c0de111/inki/images/4_2_white_pages/esign_4_2_page_3.JPG

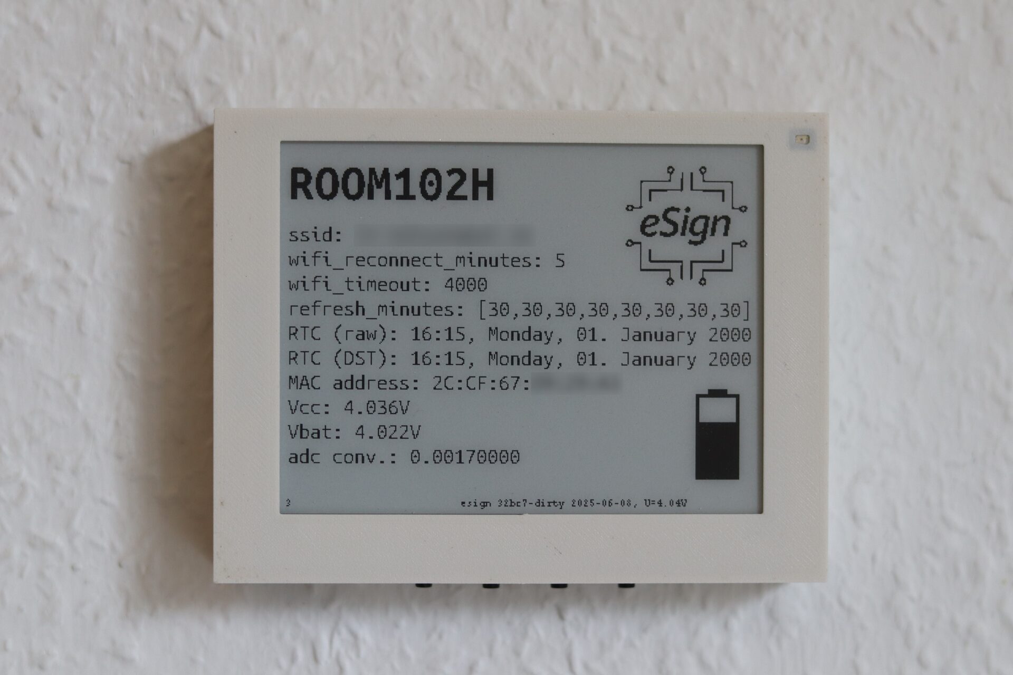
images/4_2_white_pages/esign_4_2_page_3.JPG
