c0de111/inki/images/7_5_ccu-historian.JPG

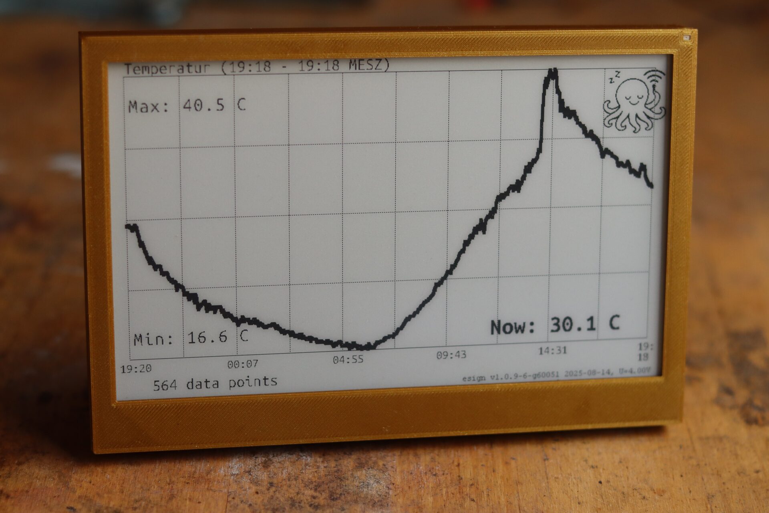
images/7_5_ccu-historian.JPG
