c0de111/inki/images/esign_4_2_backside.JPG

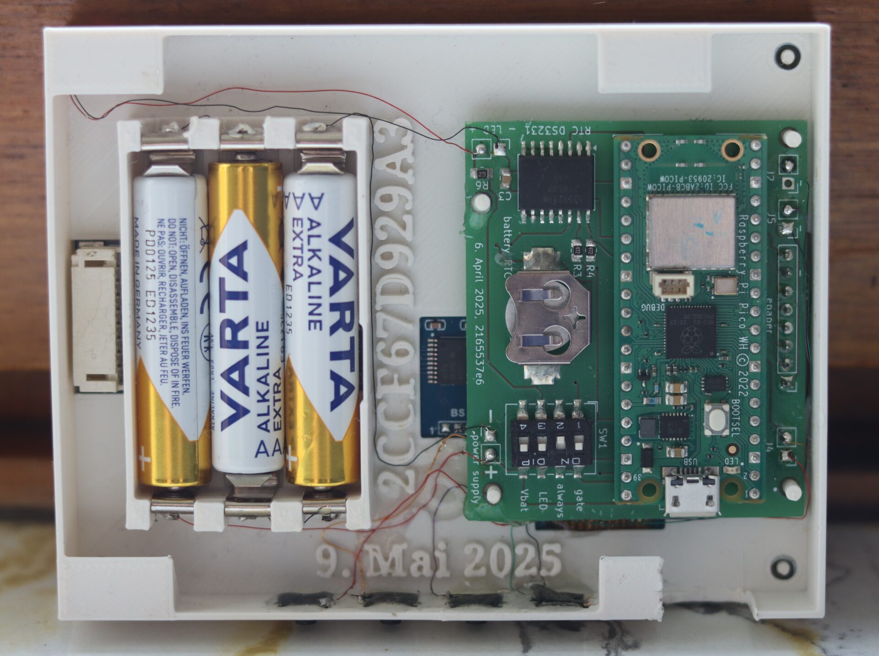
images/esign_4_2_backside.JPG
