c0de111/inki/images/esign_4_2_video_refresh_screenshot.png

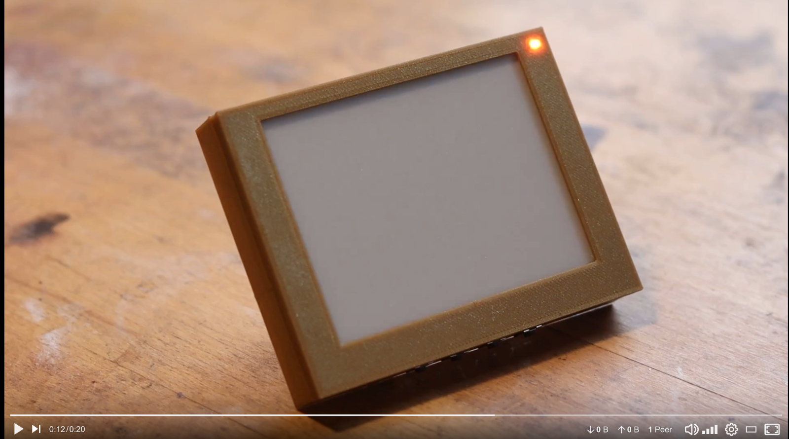
images/esign_4_2_video_refresh_screenshot.png
