c0de111/inki/images/esign_4_2_video_screenshot.jpg

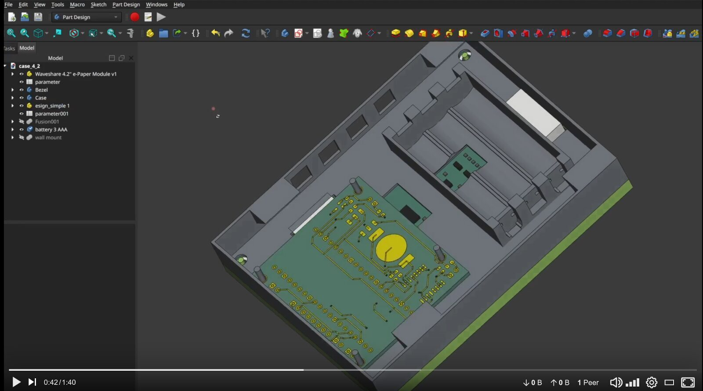
images/esign_4_2_video_screenshot.jpg
