c0de111/inki/images/inki_octopus.png

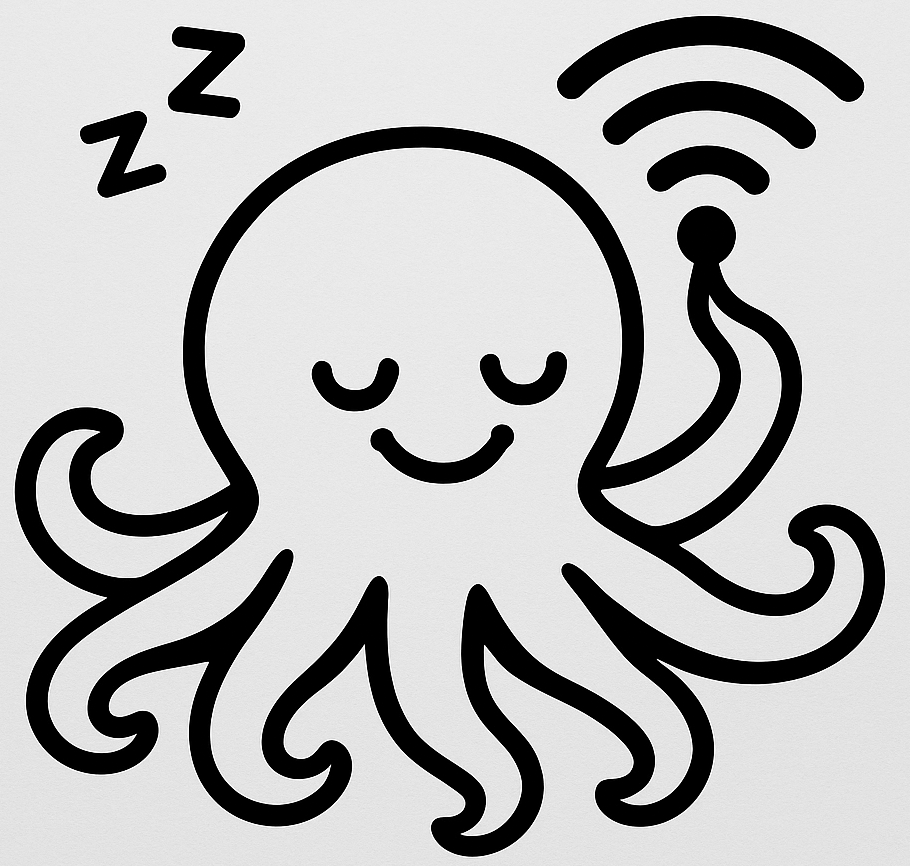
images/inki_octopus.png
