c0de111/inki/images/inki_webinterface_landingpage_combined.png

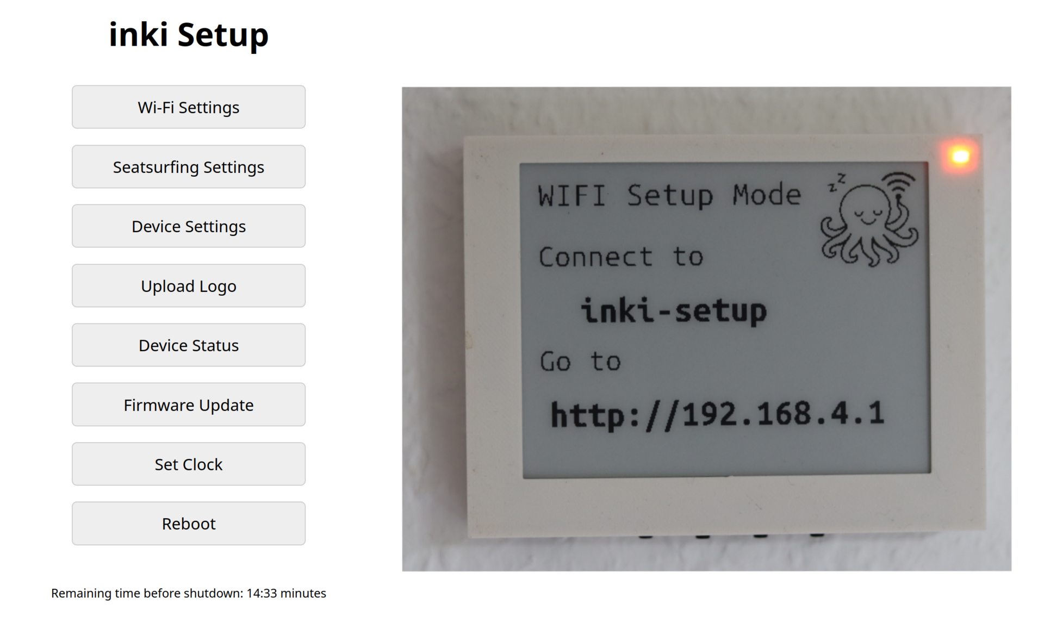
images/inki_webinterface_landingpage_combined.png
