c0de111/inki/images/log_prototype_esign_7_5.png

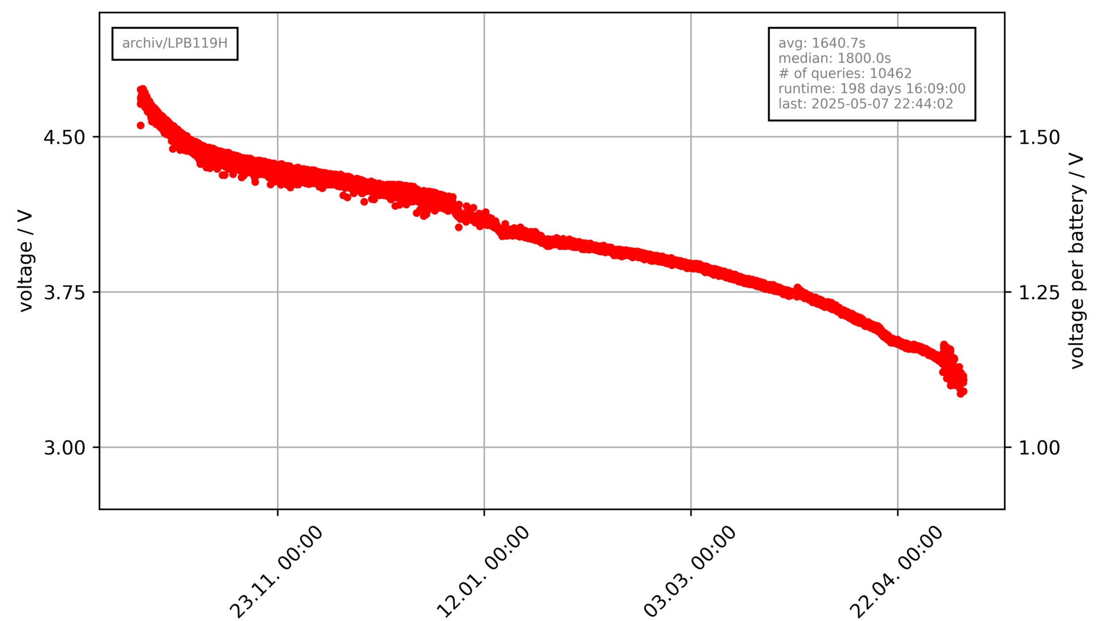
images/log_prototype_esign_7_5.png
