c0de111/inki/firmware/c/ImageResources.c

#include "ImageResources.h"

// Image arrays and constants
const SubImage battery_levels_64x97[] = {
    { .data = gImage_battery_level_1, .width = 64, .height = 97 },
    { .data = gImage_battery_level_2, .width = 64, .height = 97 },
    { .data = gImage_battery_level_3, .width = 64, .height = 97 },
    { .data = gImage_battery_level_4, .width = 64, .height = 97 },
    { .data = gImage_battery_level_5, .width = 64, .height = 97 },
    { .data = gImage_battery_level_6, .width = 64, .height = 97 },
    { .data = gImage_battery_level_7, .width = 64, .height = 97 },
    { .data = gImage_battery_level_8, .width = 64, .height = 97 },
    { .data = gImage_battery_level_9, .width = 64, .height = 97 },
    { .data = gImage_battery_level_10, .width = 64, .height = 97 },
};

const SubImage inki_octopus_100_95 = {
    .data = gImage_inki_octopus_100_95,
    .width = 104,
    .height = 95
};

const SubImage qr_github_link = {
    .data = gImage_github_link,
    .width = 56,
    .height = 50
};

const unsigned char gImage_battery_level_1[776] = {
    0x00, 0x00, 0x00, 0x00, 0x00, 0x00, 0x00, 0x00, 0x00, 0x00, 0x00, 0x00, 0x00, 0x00, 0x00, 0x00,
    0x00, 0x00, 0x00, 0x00, 0x00, 0x00, 0x00, 0x00, 0x00, 0x00, 0x00, 0x00, 0x00, 0x00, 0x00, 0x00,
    0x00, 0x00, 0x00, 0x00, 0x00, 0x00, 0x00, 0x00, 0x00, 0x00, 0x00, 0x00, 0x00, 0x00, 0x00, 0x00,
    0x00, 0x00, 0x00, 0x00, 0x00, 0x00, 0x00, 0x00, 0x00, 0x00, 0x00, 0x00, 0x00, 0x00, 0x00, 0x00,
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
    0x00, 0x00, 0x00, 0x00, 0x06, 0x00, 0x18, 0x60, 0x03, 0xF8, 0x0C, 0x01, 0x83, 0x00, 0x00, 0x00,
    0x00, 0x06, 0x00, 0x0F, 0xC0, 0x01, 0xF0, 0x0C, 0x01, 0x83, 0x00, 0x00, 0x00, 0x00, 0x06, 0x00,
    0x07, 0x80, 0x00, 0x00, 0x18, 0x03, 0x03, 0x00, 0x00, 0x01, 0xF0, 0x03, 0x00, 0x00, 0x00, 0x00,
    0x00, 0x18, 0x07, 0x02, 0x00, 0x00, 0x07, 0xF8, 0x03, 0x00, 0x00, 0x00, 0x00, 0x00, 0x18, 0x06,
    0x06, 0x00, 0x00, 0x0E, 0x18, 0x03, 0x80, 0x00, 0x60, 0x03, 0x00, 0x30, 0x1C, 0x06, 0x00, 0x00,
    0x1C, 0x38, 0x01, 0x80, 0x00, 0x60, 0x03, 0x00, 0x30, 0x38, 0x0C, 0x00, 0x00, 0x18, 0x70, 0x01,
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
};
