c0de111/inki/firmware/c/rv3028.c

#include "rv3028.h"

#include <stddef.h>
#include <string.h>

#define RV3028_REG_SECONDS 0x00u
#define RV3028_REG_MINUTES 0x01u
#define RV3028_REG_HOURS 0x02u
#define RV3028_REG_WEEKDAY 0x03u
#define RV3028_REG_DATE 0x04u
#define RV3028_REG_MONTH 0x05u
#define RV3028_REG_YEAR 0x06u

#define RV3028_REG_MINUTES_ALARM 0x07u
#define RV3028_REG_HOURS_ALARM 0x08u
#define RV3028_REG_WEEKDAY_DATE_ALARM 0x09u

#define RV3028_REG_STATUS 0x0Eu
#define RV3028_REG_CONTROL1 0x0Fu
#define RV3028_REG_CONTROL2 0x10u
#define RV3028_REG_EEPROM_BACKUP 0x37u
#define RV3028_REG_ID 0x28u

#define RV3028_STATUS_AF_BIT (1u << 2)

#define RV3028_CONTROL1_WADA_BIT (1u << 5)
#define RV3028_CONTROL2_AIE_BIT (1u << 3)
#define RV3028_CONTROL2_12_24_BIT (1u << 1)

#define RV3028_BACKUP_FEDE_BIT (1u << 4)
#define RV3028_BACKUP_BSM_MASK (3u << 2)
#define RV3028_BACKUP_BSM_LSM (3u << 2)

static uint8_t bcd_to_bin(uint8_t value) {
    return (uint8_t)(((value >> 4u) * 10u) + (value & 0x0Fu));
}

static uint8_t bin_to_bcd(uint8_t value) {
    return (uint8_t)(((value / 10u) << 4u) | (value % 10u));
}

static bool bcd_value_in_range(uint8_t bcd, uint8_t min_value, uint8_t max_value) {
    const uint8_t low = (uint8_t)(bcd & 0x0Fu);
    const uint8_t high = (uint8_t)((bcd >> 4u) & 0x0Fu);
    if (low > 9u || high > 9u) {
        return false;
    }

    const uint8_t value = bcd_to_bin(bcd);
    return (value >= min_value) && (value <= max_value);
}

static int rv3028_read_bytes(rv3028_t *rtc, uint8_t reg, uint8_t *data, size_t len) {
    if (!rtc || !rtc->i2c || !data || len == 0u) {
        return -1;
    }

    const int write_rc = i2c_write_blocking(rtc->i2c, rtc->addr, &reg, 1, true);
    if (write_rc != 1) {
        return -2;
    }

    const int read_rc = i2c_read_blocking(rtc->i2c, rtc->addr, data, len, false);
    if (read_rc != (int)len) {
        return -3;
    }

    return 0;
}

static int rv3028_write_bytes(rv3028_t *rtc, uint8_t reg, const uint8_t *data, size_t len) {
    if (!rtc || !rtc->i2c || !data || len == 0u || len > 15u) {
        return -1;
    }

    uint8_t buffer[16];
    buffer[0] = reg;
    memcpy(&buffer[1], data, len);

    const int write_rc = i2c_write_blocking(rtc->i2c, rtc->addr, buffer, len + 1u, false);
    if (write_rc != (int)(len + 1u)) {
        return -2;
    }

    return 0;
}

static int rv3028_read_u8(rv3028_t *rtc, uint8_t reg, uint8_t *value) {
    return rv3028_read_bytes(rtc, reg, value, 1u);
}

static int rv3028_write_u8(rv3028_t *rtc, uint8_t reg, uint8_t value) {
    return rv3028_write_bytes(rtc, reg, &value, 1u);
}

static int rv3028_configure_backup_switchover(rv3028_t *rtc) {
    uint8_t backup = 0u;
    int rc = rv3028_read_u8(rtc, RV3028_REG_EEPROM_BACKUP, &backup);
    if (rc != 0) {
        return rc;
    }

    uint8_t updated = backup;
    updated = (uint8_t)(updated | RV3028_BACKUP_FEDE_BIT);               // FEDE = 1
    updated = (uint8_t)((updated & (uint8_t)(~RV3028_BACKUP_BSM_MASK)) | // BSM = 11 (LSM)
                        RV3028_BACKUP_BSM_LSM);

    if (updated == backup) {
        return 0;
    }

    return rv3028_write_u8(rtc, RV3028_REG_EEPROM_BACKUP, updated);
}

int rv3028_init(rv3028_t *rtc, i2c_inst_t *i2c, uint8_t addr) {
    if (!rtc || !i2c) {
        return -1;
    }

    rtc->i2c = i2c;
    rtc->addr = (addr == 0u) ? RV3028_ADDR_DEFAULT : addr;
    const int rc = rv3028_configure_backup_switchover(rtc);
    if (rc != 0) {
        return rc;
    }
    return 0;
}

int rv3028_read_time(rv3028_t *rtc, rv3028_time_t *time_data) {
    if (!time_data) {
        return -1;
    }

    uint8_t raw[7] = {0};
    int rc = rv3028_read_bytes(rtc, RV3028_REG_SECONDS, raw, sizeof(raw));
    if (rc != 0) {
        return rc;
    }

    uint8_t control2 = 0u;
    rc = rv3028_read_u8(rtc, RV3028_REG_CONTROL2, &control2);
    if (rc != 0) {
        return rc;
    }
    const bool use_12h_mode = (control2 & RV3028_CONTROL2_12_24_BIT) != 0u;

    const uint8_t sec_bcd = (uint8_t)(raw[0] & 0x7Fu);
    const uint8_t min_bcd = (uint8_t)(raw[1] & 0x7Fu);
    if (!bcd_value_in_range(sec_bcd, 0u, 59u) || !bcd_value_in_range(min_bcd, 0u, 59u)) {
        return -4;
    }

    uint8_t hour = 0u;
    if (use_12h_mode) {
        const bool is_pm = (raw[2] & 0x20u) != 0u;
        const uint8_t hour12_bcd = (uint8_t)(raw[2] & 0x1Fu);
        if (!bcd_value_in_range(hour12_bcd, 1u, 12u)) {
            return -5;
        }
        hour = bcd_to_bin(hour12_bcd);
        if (hour == 12u) {
            hour = 0u;
        }
        if (is_pm) {
            hour = (uint8_t)(hour + 12u);
        }
    } else {
        const uint8_t hour_bcd = (uint8_t)(raw[2] & 0x3Fu);
        if (!bcd_value_in_range(hour_bcd, 0u, 23u)) {
            return -5;
        }
        hour = bcd_to_bin(hour_bcd);
    }

    const uint8_t weekday = (uint8_t)(raw[3] & 0x07u);
    if (weekday > 6u) {
        return -6;
    }

    const uint8_t date_bcd = (uint8_t)(raw[4] & 0x3Fu);
    const uint8_t month_bcd = (uint8_t)(raw[5] & 0x1Fu);
    const uint8_t year_bcd = raw[6];

    if (!bcd_value_in_range(date_bcd, 1u, 31u) || !bcd_value_in_range(month_bcd, 1u, 12u) ||
        !bcd_value_in_range(year_bcd, 0u, 99u)) {
        return -7;
    }

    time_data->seconds = bcd_to_bin(sec_bcd);
    time_data->minutes = bcd_to_bin(min_bcd);
    time_data->hours = hour;
    time_data->day = (uint8_t)(weekday + 1u); // map RV weekday 0..6 to internal 1..7
    time_data->date = bcd_to_bin(date_bcd);
    time_data->month = bcd_to_bin(month_bcd);
    time_data->year = bcd_to_bin(year_bcd);

    return 0;
}

int rv3028_set_time(rv3028_t *rtc, const rv3028_time_t *time_data) {
    if (!time_data) {
        return -1;
    }

    if (time_data->seconds > 59u || time_data->minutes > 59u || time_data->hours > 23u ||
        time_data->day < 1u || time_data->day > 7u || time_data->date < 1u ||
        time_data->date > 31u || time_data->month < 1u || time_data->month > 12u ||
        time_data->year > 99u) {
        return -2;
    }

    uint8_t control2 = 0u;
    int rc = rv3028_read_u8(rtc, RV3028_REG_CONTROL2, &control2);
    if (rc != 0) {
        return rc;
    }

    control2 = (uint8_t)(control2 & (uint8_t)(~RV3028_CONTROL2_12_24_BIT)); // force 24h mode
    rc = rv3028_write_u8(rtc, RV3028_REG_CONTROL2, control2);
    if (rc != 0) {
        return rc;
    }

    uint8_t encoded[7] = {0};
    encoded[0] = bin_to_bcd(time_data->seconds);
    encoded[1] = bin_to_bcd(time_data->minutes);
    encoded[2] = (uint8_t)(bin_to_bcd(time_data->hours) & 0x3Fu);
    encoded[3] = (uint8_t)((time_data->day - 1u) & 0x07u); // map internal 1..7 to RV weekday 0..6
    encoded[4] = (uint8_t)(bin_to_bcd(time_data->date) & 0x3Fu);
    encoded[5] = (uint8_t)(bin_to_bcd(time_data->month) & 0x1Fu);
    encoded[6] = bin_to_bcd(time_data->year);

    return rv3028_write_bytes(rtc, RV3028_REG_SECONDS, encoded, sizeof(encoded));
}

int rv3028_set_daily_alarm_hour_minute(rv3028_t *rtc, uint8_t hour, uint8_t minute) {
    if (hour > 23u || minute > 59u) {
        return -1;
    }

    uint8_t control1 = 0u;
    int rc = rv3028_read_u8(rtc, RV3028_REG_CONTROL1, &control1);
    if (rc != 0) {
        return rc;
    }

    control1 =
        (uint8_t)(control1 & (uint8_t)(~RV3028_CONTROL1_WADA_BIT)); // weekday/date mode default
    rc = rv3028_write_u8(rtc, RV3028_REG_CONTROL1, control1);
    if (rc != 0) {
        return rc;
    }

    uint8_t alarm_data[3] = {0};
    alarm_data[0] = (uint8_t)(bin_to_bcd(minute) & 0x7Fu); // AE_M = 0 (enabled)
    alarm_data[1] = (uint8_t)(bin_to_bcd(hour) & 0x3Fu);   // AE_H = 0 (enabled), 24h mode
    alarm_data[2] = 0x80u;                                 // AE_WD = 1 (disabled) => daily alarm

    return rv3028_write_bytes(rtc, RV3028_REG_MINUTES_ALARM, alarm_data, sizeof(alarm_data));
}

int rv3028_enable_alarm_interrupt(rv3028_t *rtc, bool enable) {
    uint8_t control2 = 0u;
    int rc = rv3028_read_u8(rtc, RV3028_REG_CONTROL2, &control2);
    if (rc != 0) {
        return rc;
    }

    if (enable) {
        control2 = (uint8_t)(control2 | RV3028_CONTROL2_AIE_BIT);
    } else {
        control2 = (uint8_t)(control2 & (uint8_t)(~RV3028_CONTROL2_AIE_BIT));
    }

    return rv3028_write_u8(rtc, RV3028_REG_CONTROL2, control2);
}

int rv3028_read_alarm_flag(rv3028_t *rtc, bool *flag_set) {
    uint8_t status = 0u;
    int rc = rv3028_read_u8(rtc, RV3028_REG_STATUS, &status);
    if (rc != 0) {
        return rc;
    }
    *flag_set = (status & RV3028_STATUS_AF_BIT) != 0u;
    return 0;
}

int rv3028_clear_alarm_flag(rv3028_t *rtc) {
    uint8_t status = 0u;
    int rc = rv3028_read_u8(rtc, RV3028_REG_STATUS, &status);
    if (rc != 0) {
        return rc;
    }

    status = (uint8_t)(status & (uint8_t)(~RV3028_STATUS_AF_BIT));
    return rv3028_write_u8(rtc, RV3028_REG_STATUS, status);
}
